robdobsn/JewelryOS/evaluations/HRMAnalysis/data/20240518_2_HRM_ADC_FromMAX30101.csv

Time (s)Time (s) | Red | IR
1110.2521249.873 | 2812238 | 3092781
1110.2921249.913 | 2812442 | 3093248
1110.3321249.957 | 2812617 | 3093659
1110.3721249.997 | 2812752 | 3094058
1110.4121250.037 | 2812865 | 3094396
1110.4531250.077 | 2812965 | 3094645
1110.4931250.117 | 2812974 | 3094581
1110.5331250.157 | 2812728 | 3093739
1110.5731250.197 | 2812510 | 3093014
1110.6131250.237 | 2812484 | 3092845
1110.6561250.277 | 2812517 | 3092910
1110.6961250.317 | 2812620 | 3093115
1110.7361250.362 | 2812736 | 3093443
1110.7761250.402 | 2812939 | 3093964
1110.8161250.442 | 2813105 | 3094398
1110.8621250.482 | 2813203 | 3094640
1110.9021250.522 | 2813272 | 3094828
1110.9421250.567 | 2813317 | 3094947
1110.9821250.607 | 2813325 | 3095045
1111.0221250.647 | 2813321 | 3095096
1111.0641250.687 | 2813316 | 3095095
1111.1041250.727 | 2813286 | 3095044
1111.1441250.77 | 2813235 | 3094972
1111.1841250.81 | 2813226 | 3094989
1111.2241250.85 | 2813238 | 3095000
1111.271250.89 | 2813245 | 3095033
1111.311250.93 | 2813279 | 3095119
1111.351250.972 | 2813302 | 3095210
1111.391251.012 | 2813343 | 3095333
1111.431251.052 | 2813386 | 3095450
1111.4731251.092 | 2813365 | 3095346
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
