robdobsn/JewelryOS/evaluations/HRMAnalysis/data/20240518_3_HRM_ADC_FromMAX30101.csv

Time (s)Time (s) | Red | IR
1181.6191249.873 | 2812238 | 3092781
1181.6591249.913 | 2812442 | 3093248
1181.6991249.957 | 2812617 | 3093659
1181.7441249.997 | 2812752 | 3094058
1181.7841250.037 | 2812865 | 3094396
1181.8241250.077 | 2812965 | 3094645
1181.8641250.117 | 2812974 | 3094581
1181.9041250.157 | 2812728 | 3093739
1181.9481250.197 | 2812510 | 3093014
1181.9881250.237 | 2812484 | 3092845
1182.0281250.277 | 2812517 | 3092910
1182.0681250.317 | 2812620 | 3093115
1182.1081250.362 | 2812736 | 3093443
1182.151250.402 | 2812939 | 3093964
1182.191250.442 | 2813105 | 3094398
1182.231250.482 | 2813203 | 3094640
1182.271250.522 | 2813272 | 3094828
1182.311250.567 | 2813317 | 3094947
1182.351250.607 | 2813325 | 3095045
1182.391250.647 | 2813321 | 3095096
1182.431250.687 | 2813316 | 3095095
1182.471250.727 | 2813286 | 3095044
1182.511250.77 | 2813235 | 3094972
1182.5551250.81 | 2813226 | 3094989
1182.5951250.85 | 2813238 | 3095000
1182.6351250.89 | 2813245 | 3095033
1182.6751250.93 | 2813279 | 3095119
1182.7151250.972 | 2813302 | 3095210
1182.7551251.012 | 2813343 | 3095333
1182.7591251.052 | 2813386 | 3095450
1182.7991251.092 | 2813365 | 3095346
1182.8391251.132 | 2813131 | 3094600
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
