robdobsn/JewelryOS/evaluations/HRMAnalysis/data/20240518_4_HRM_ADC_FromMAX30101.csv

Time (s) | Red | IR
1249.873 | 2812238 | 3092781
1249.913 | 2812442 | 3093248
1249.957 | 2812617 | 3093659
1249.997 | 2812752 | 3094058
1250.037 | 2812865 | 3094396
1250.077 | 2812965 | 3094645
1250.117 | 2812974 | 3094581
1250.157 | 2812728 | 3093739
1250.197 | 2812510 | 3093014
1250.237 | 2812484 | 3092845
1250.277 | 2812517 | 3092910
1250.317 | 2812620 | 3093115
1250.362 | 2812736 | 3093443
1250.402 | 2812939 | 3093964
1250.442 | 2813105 | 3094398
1250.482 | 2813203 | 3094640
1250.522 | 2813272 | 3094828
1250.567 | 2813317 | 3094947
1250.607 | 2813325 | 3095045
1250.647 | 2813321 | 3095096
1250.687 | 2813316 | 3095095
1250.727 | 2813286 | 3095044
1250.77 | 2813235 | 3094972
1250.81 | 2813226 | 3094989
1250.85 | 2813238 | 3095000
1250.89 | 2813245 | 3095033
1250.93 | 2813279 | 3095119
1250.972 | 2813302 | 3095210
1251.012 | 2813343 | 3095333
1251.052 | 2813386 | 3095450
1251.092 | 2813365 | 3095346
1251.132 | 2813131 | 3094600
1251.174 | 2812854 | 3093700
1251.214 | 2812766 | 3093420
1251.254 | 2812758 | 3093381
1251.294 | 2812766 | 3093423
1251.334 | 2812804 | 3093563
1251.381 | 2812880 | 3093763
1251.421 | 2812890 | 3093815
1251.461 | 2812889 | 3093830
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
