robdobsn/JewelryOS/components/hardware/LEDHeart/LEDHeart.h

/////////////////////////////////////////////////////////////////////////////////////////////////////////////////
//
// LED Heart Display
//
// Rob Dobson 2023
//
/////////////////////////////////////////////////////////////////////////////////////////////////////////////////

#pragma once

#include <vector>
#include <RaftJsonIF.h>

class LEDHeart
{
public:
    // Constructor / Destructor
    LEDHeart();
    ~LEDHeart();

    // Setup
    void setup(const RaftJsonIF& config);

    // Loop
    void loop();

    // Get time to next animation step
    uint32_t getTimeToNextAnimStepUs();

    // Start pulse animation
    void startPulseAnimation()
    {
        _nextAnimStepAfterUs = _animStepTimeUs;
        _animationStepNum = 0;
    }

private:

    // Brightness level % (0-100)
    uint32_t _displayBrightnessPC = 100;

    // LED pins and intensity factors
    std::vector<int> _ledPins;
    std::vector<int> _ledIntensityFactors;

    // Active level
    bool _ledActiveLevel = false;

    // Timer for animation
    uint64_t _lastAnimTimeUs = 0;

    // Animation step timing
    static const uint32_t ANIM_STEP_TIME_US_DEFAULT = 25000;
    uint32_t _animStepTimeUs = ANIM_STEP_TIME_US_DEFAULT;

    // Next animation step time
    uint32_t _nextAnimStepAfterUs = ANIM_STEP_TIME_US_DEFAULT;

    // Animation step number
    uint32_t _animationStepNum = 0;

    // Animation off times for LEDs
    std::vector<uint32_t> _animationOffAfterUs;

    // Animation step levels
    static const uint8_t OFF_LEVEL = 0;
    static const uint8_t LOW_LEVEL = 1;
    static const uint8_t MID_LEVEL = 2;
    static const uint8_t HIGH_LEVEL = 3;
    std::vector<uint8_t> _animationStepLevels = 
    {
        LOW_LEVEL, MID_LEVEL, HIGH_LEVEL, MID_LEVEL, LOW_LEVEL, OFF_LEVEL
    };

    // Animation level count
    uint32_t _animationCount = 0;

    // Helpers
    void handleAnimationStep();

    // Debug
    static constexpr const char* MODULE_PREFIX = "LEDHeart";
};
